cormoran/dya2-keyboard/docs/src/content/docs/build-guide/v1/img/assembly/2_bottom_case_overview.jpeg

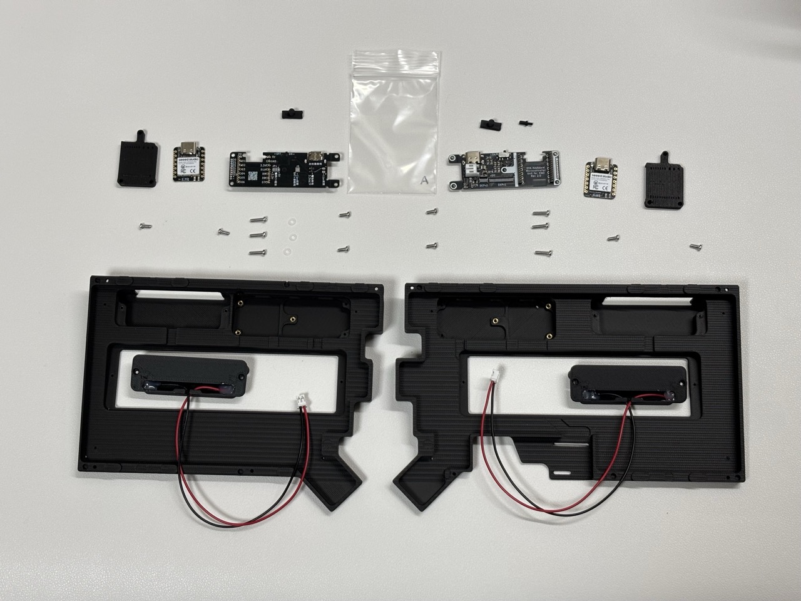
docs/src/content/docs/build-guide/v1/img/assembly/2_bottom_case_overview.jpeg
