cormoran/dya2-keyboard/docs/src/content/docs/build-guide/v1/img/assembly/4_trackball_parts.jpeg

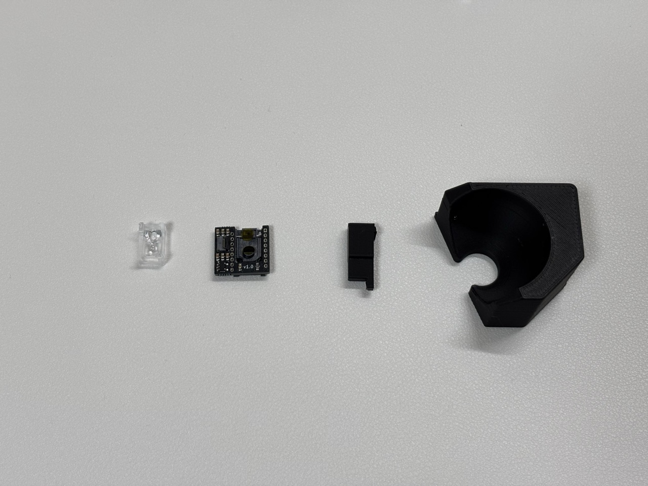
docs/src/content/docs/build-guide/v1/img/assembly/4_trackball_parts.jpeg
