cormoran/dya2-keyboard/docs/src/content/docs/build-guide/v1/img/preparation_electric_parts.jpeg

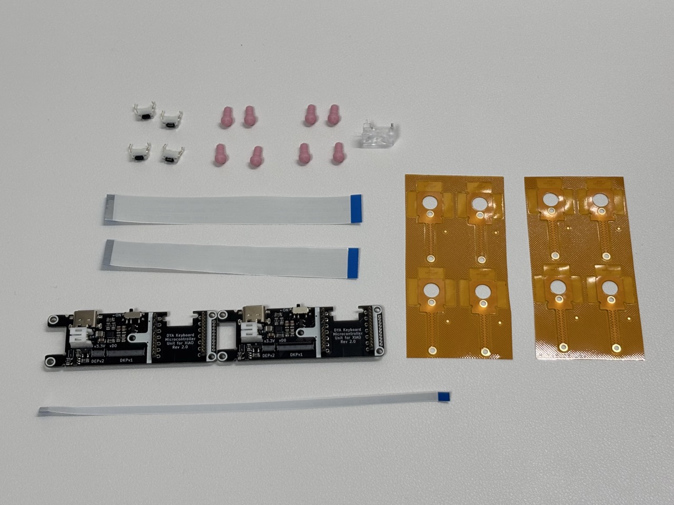
docs/src/content/docs/build-guide/v1/img/preparation_electric_parts.jpeg
