cormoran/dya2-keyboard/docs/src/content/docs/build-guide/v1/img/assembly/1_1_top_plate_separated.jpeg

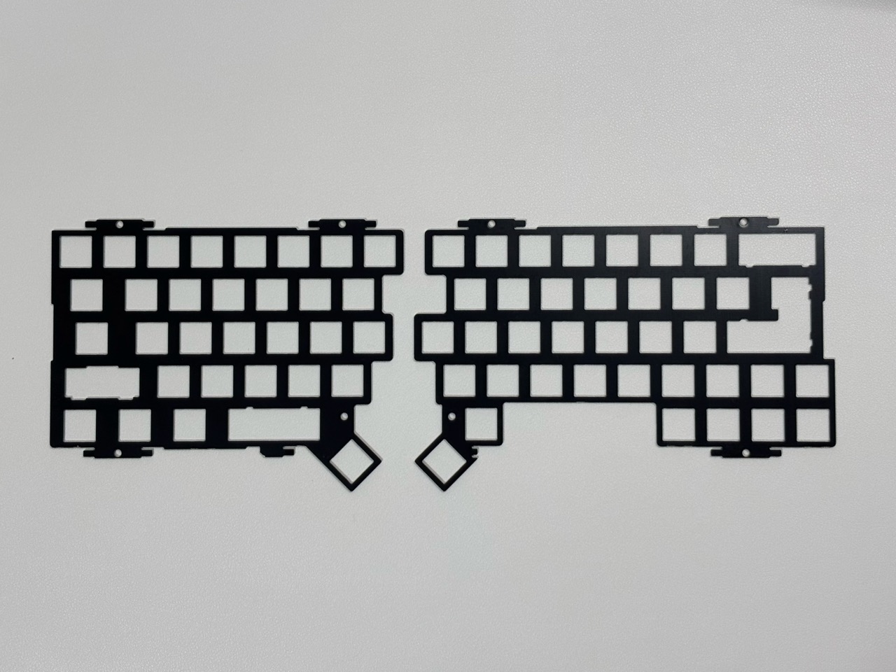
docs/src/content/docs/build-guide/v1/img/assembly/1_1_top_plate_separated.jpeg
