cormoran/dya2-keyboard/docs/src/content/docs/build-guide/v1/img/assembly/1_2_circuit_board_separated.jpeg

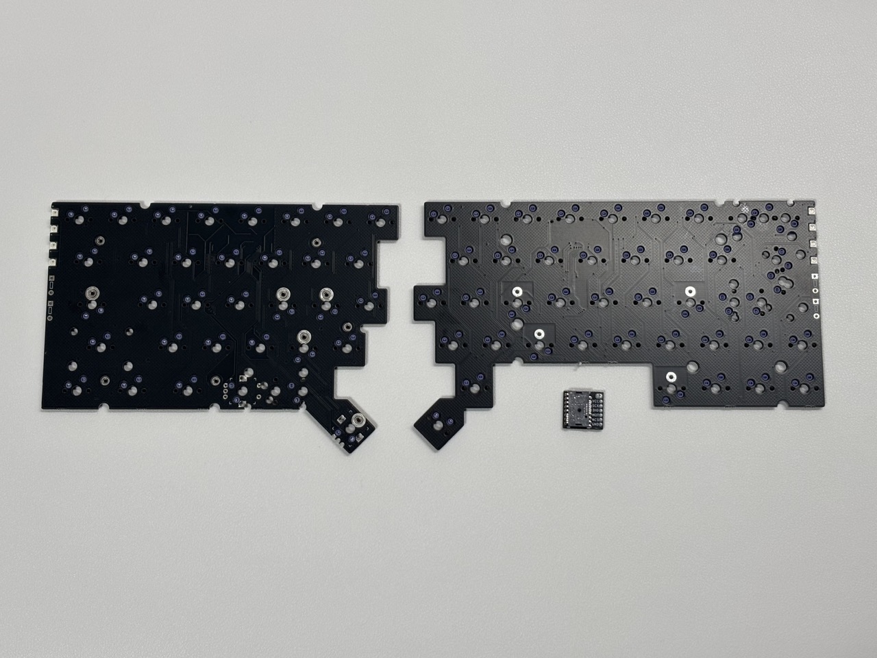
docs/src/content/docs/build-guide/v1/img/assembly/1_2_circuit_board_separated.jpeg
