cormoran/dya2-keyboard/docs/src/content/docs/build-guide/v1/img/assembly/2_1_battery_case.jpeg

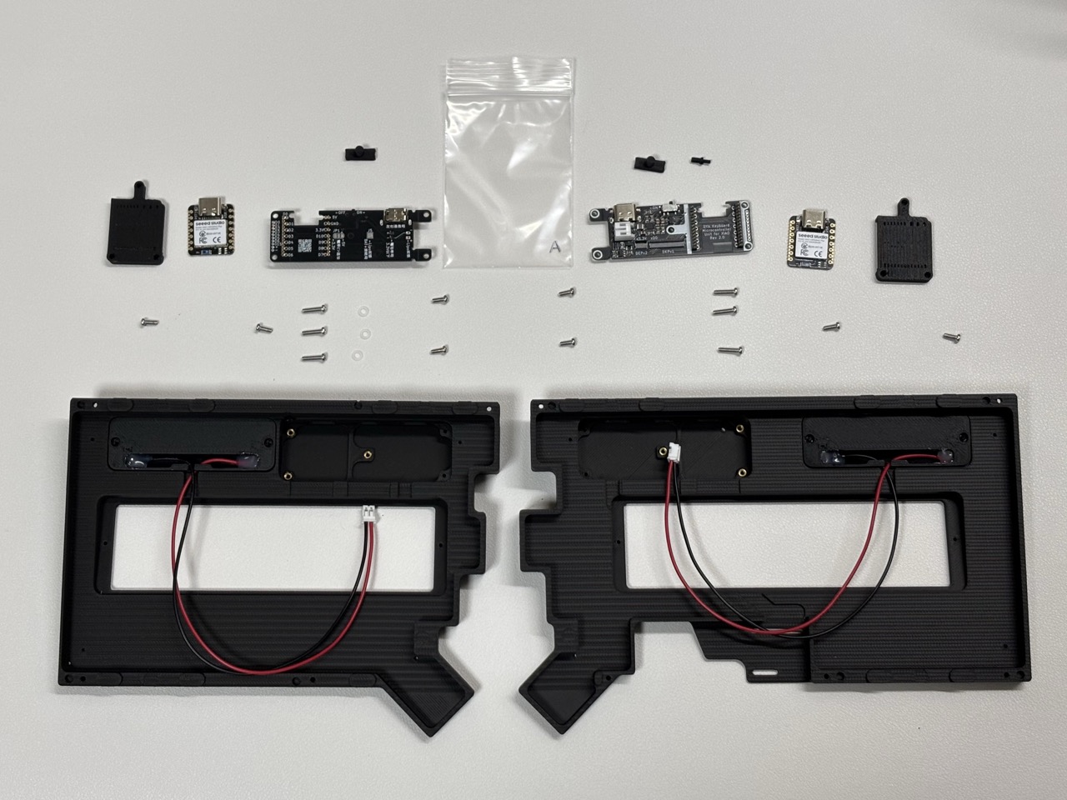
docs/src/content/docs/build-guide/v1/img/assembly/2_1_battery_case.jpeg
