cormoran/dya2-keyboard/docs/src/content/docs/build-guide/v1/img/assembly/2_1_battery_case_screwed.jpeg

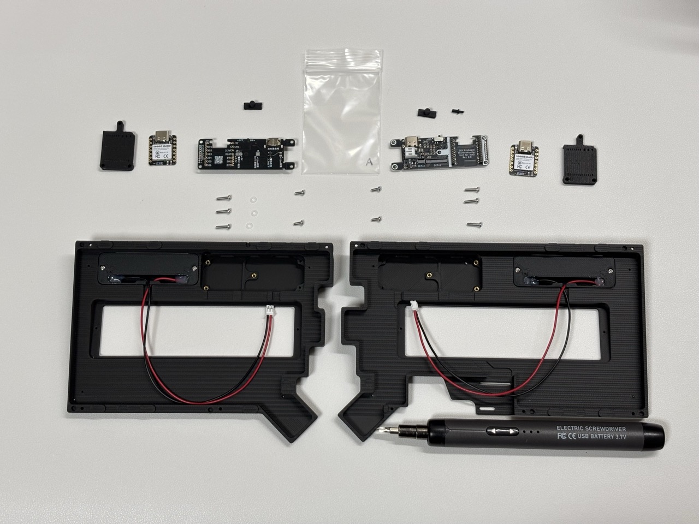
docs/src/content/docs/build-guide/v1/img/assembly/2_1_battery_case_screwed.jpeg
