cormoran/dya2-keyboard/docs/src/content/docs/build-guide/v1/img/assembly/2_2_1_xiao_attached.jpeg

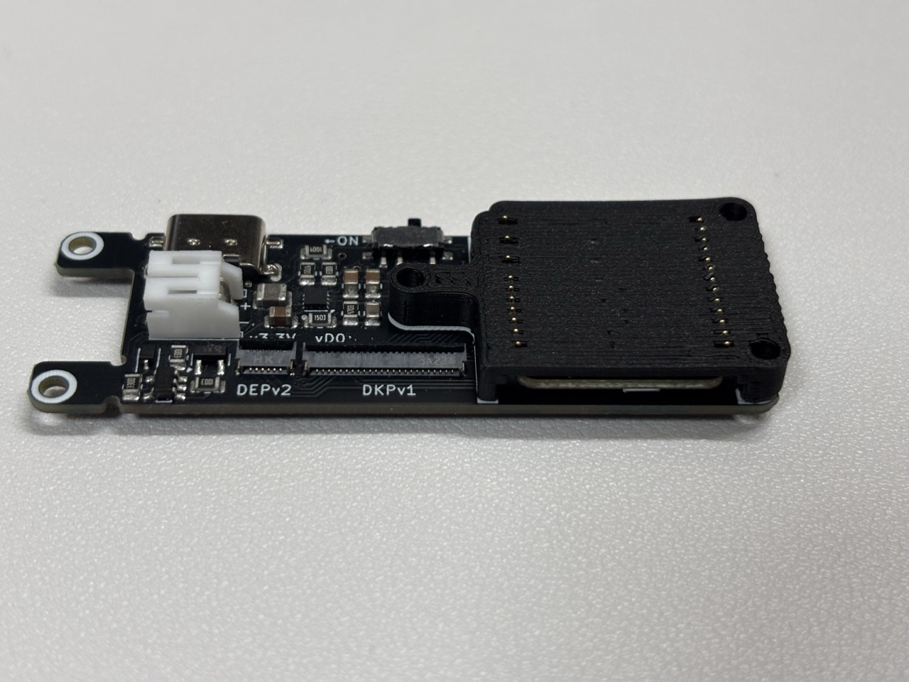
docs/src/content/docs/build-guide/v1/img/assembly/2_2_1_xiao_attached.jpeg
