cormoran/dya2-keyboard/docs/src/content/docs/build-guide/v1/img/assembly/2_2_2_power_sw.jpeg

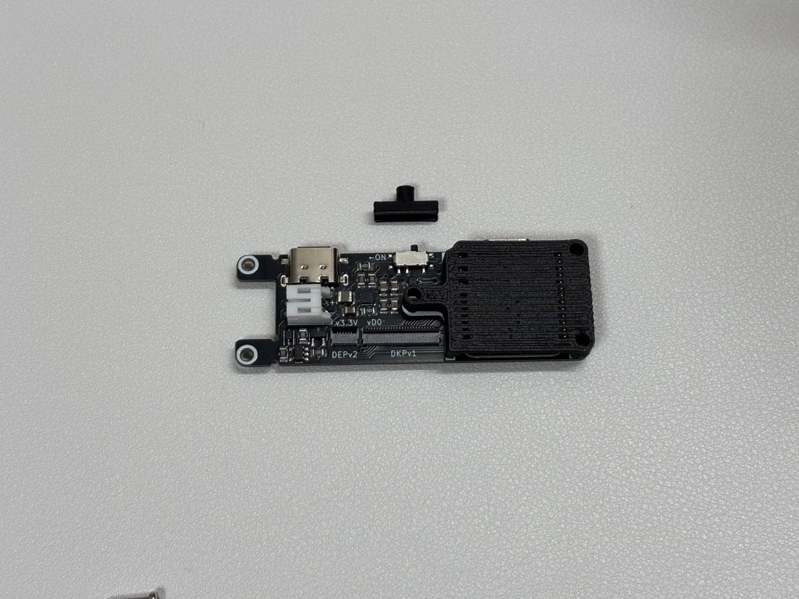
docs/src/content/docs/build-guide/v1/img/assembly/2_2_2_power_sw.jpeg
