cormoran/dya2-keyboard/docs/src/content/docs/build-guide/v1/img/assembly/2_2_3_ffc_left.jpeg

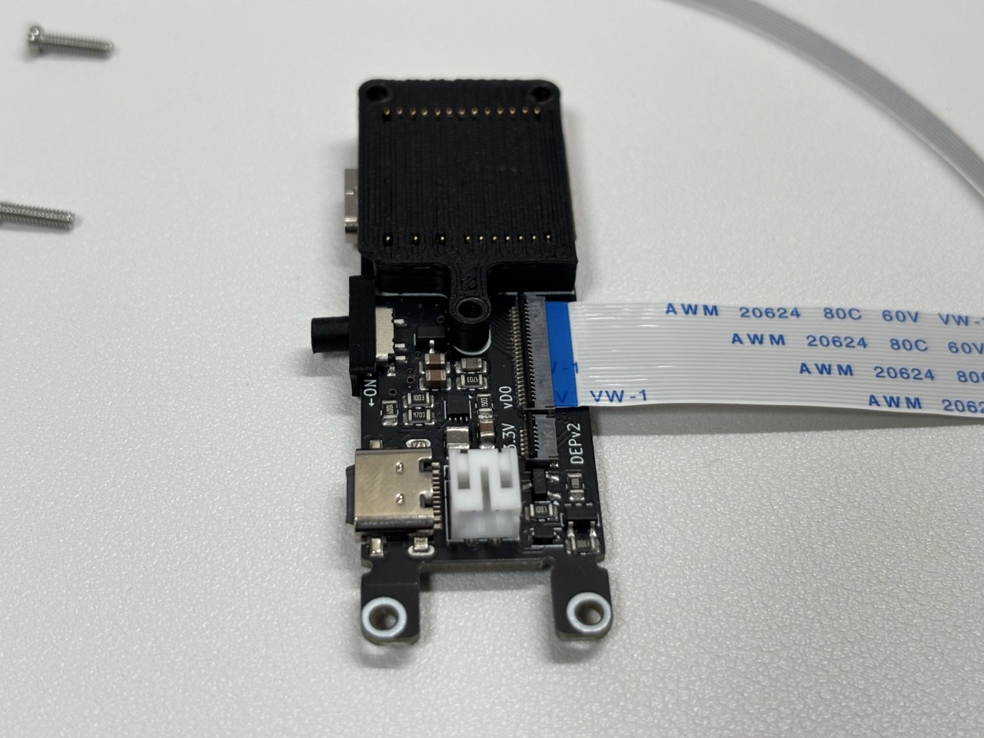
docs/src/content/docs/build-guide/v1/img/assembly/2_2_3_ffc_left.jpeg
