cormoran/dya2-keyboard/docs/src/content/docs/build-guide/v1/img/assembly/2_2_4_reset_button.jpeg

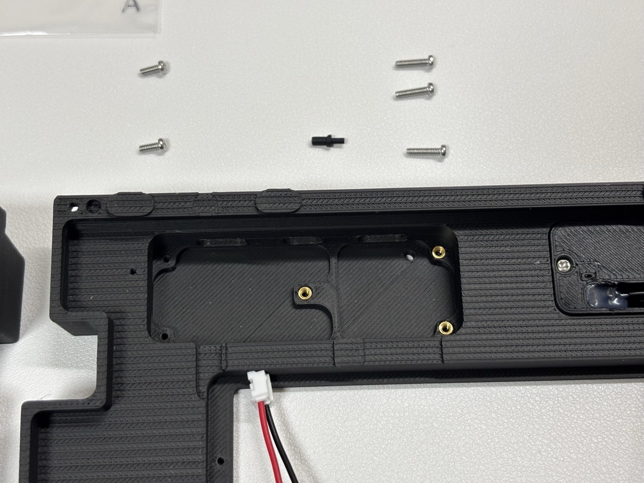
docs/src/content/docs/build-guide/v1/img/assembly/2_2_4_reset_button.jpeg
