cormoran/dya2-keyboard/docs/src/content/docs/build-guide/v1/img/assembly/2_2_5_mount_right.jpeg

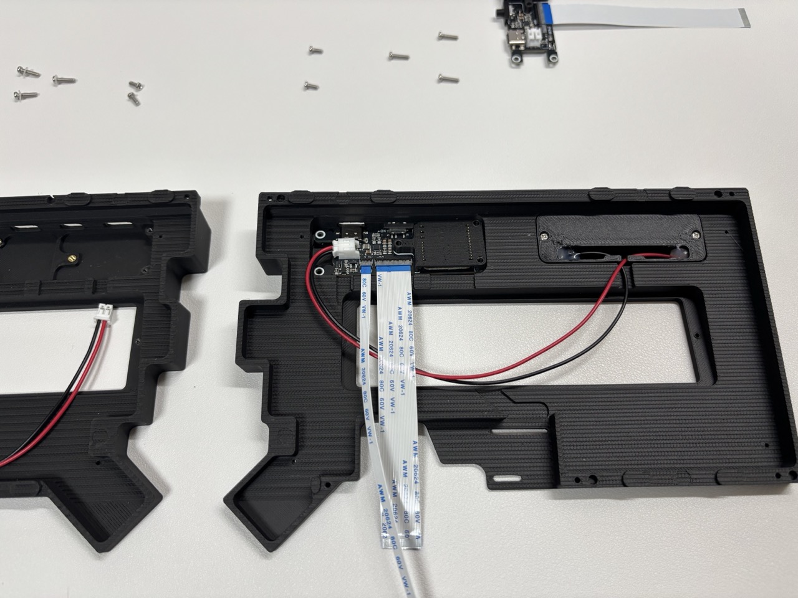
docs/src/content/docs/build-guide/v1/img/assembly/2_2_5_mount_right.jpeg
