cormoran/dya2-keyboard/docs/src/content/docs/build-guide/v1/img/assembly/2_2_6_mount_left_battery.jpeg

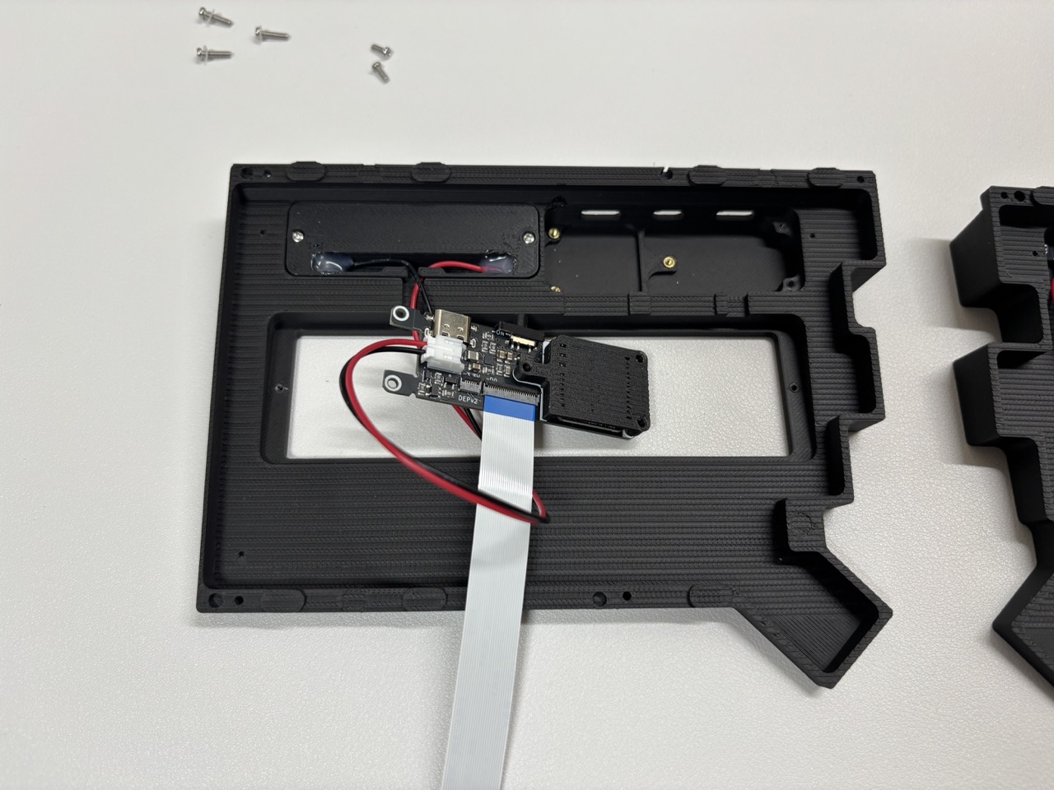
docs/src/content/docs/build-guide/v1/img/assembly/2_2_6_mount_left_battery.jpeg
