cormoran/dya2-keyboard/docs/src/content/docs/build-guide/v1/img/assembly/3_emblem_plate_bottom1.jpeg

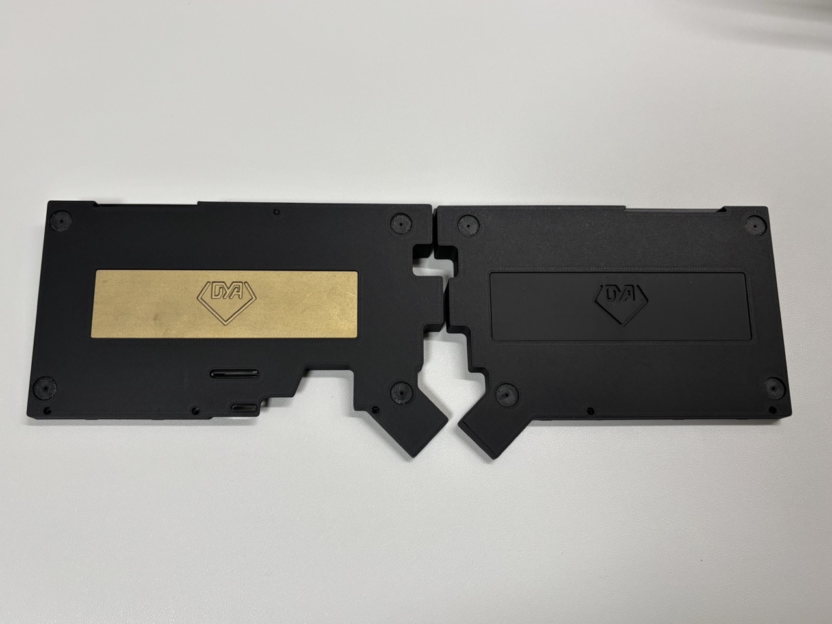
docs/src/content/docs/build-guide/v1/img/assembly/3_emblem_plate_bottom1.jpeg
