cormoran/dya2-keyboard/docs/src/content/docs/build-guide/v1/img/assembly/3_emblem_plate_bottom2.jpeg

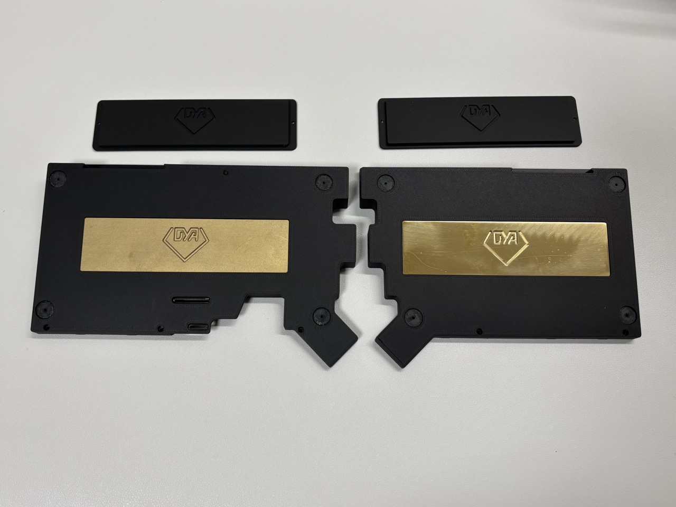
docs/src/content/docs/build-guide/v1/img/assembly/3_emblem_plate_bottom2.jpeg
