cormoran/dya2-keyboard/docs/src/content/docs/build-guide/v1/img/assembly/4_trackball_screw.jpeg

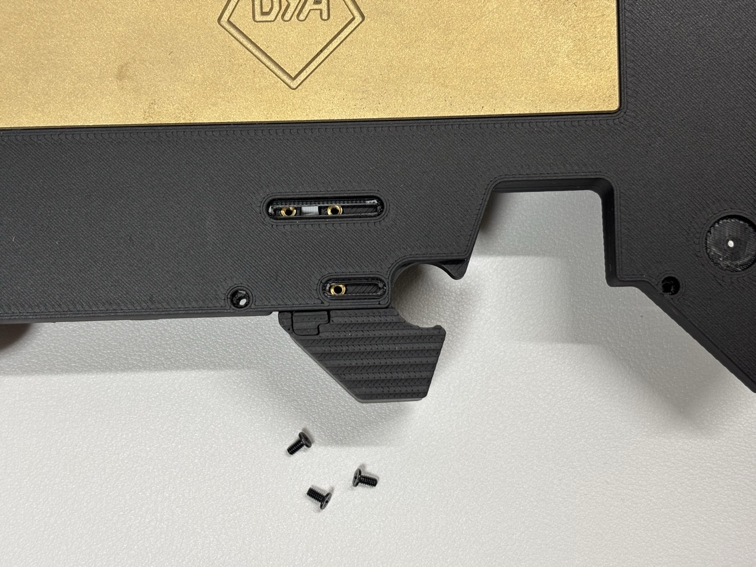
docs/src/content/docs/build-guide/v1/img/assembly/4_trackball_screw.jpeg
