cormoran/dya2-keyboard/docs/src/content/docs/build-guide/v1/img/assembly/5_1_tadpole2.jpeg

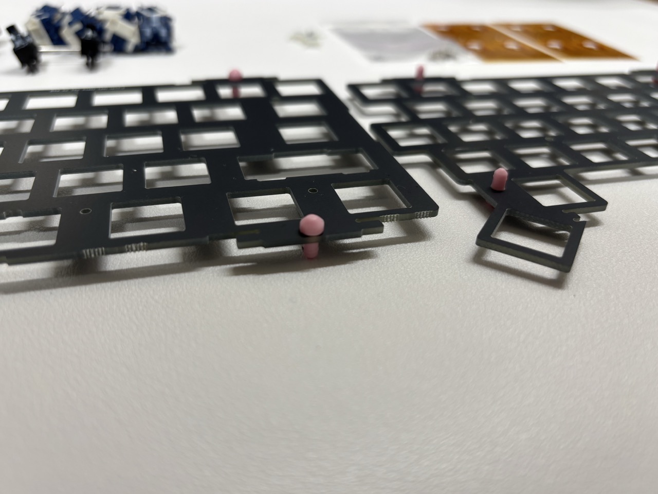
docs/src/content/docs/build-guide/v1/img/assembly/5_1_tadpole2.jpeg
