cormoran/dya2-keyboard/docs/src/content/docs/build-guide/v1/img/assembly/5_2_setting_switch_both.jpeg

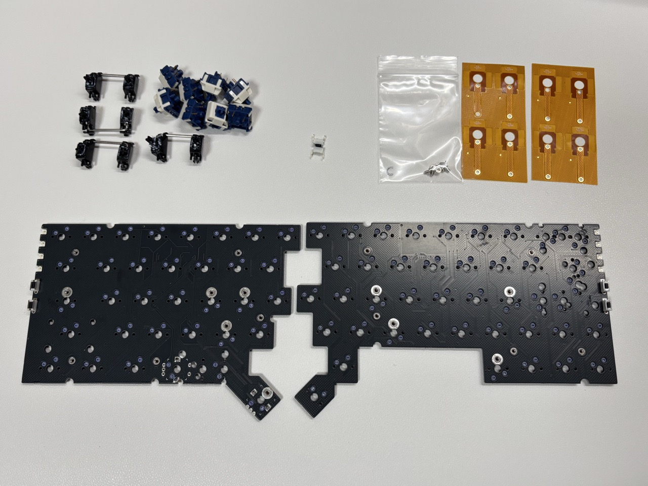
docs/src/content/docs/build-guide/v1/img/assembly/5_2_setting_switch_both.jpeg
