cormoran/dya2-keyboard/docs/src/content/docs/build-guide/v1/img/assembly/5_3_stabilizer_en.jpeg

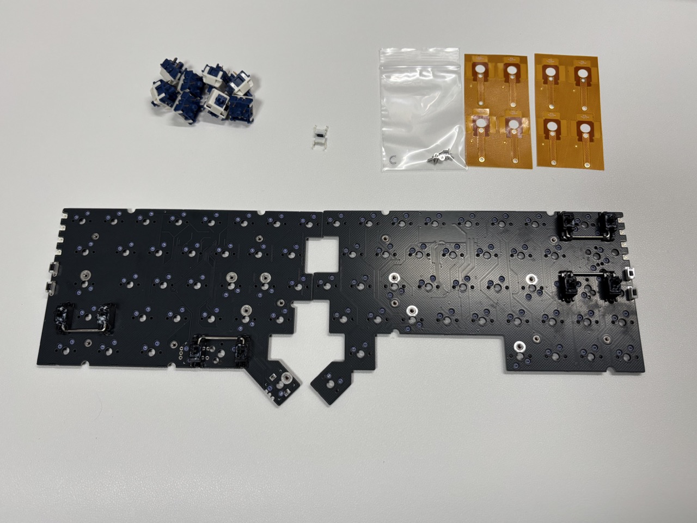
docs/src/content/docs/build-guide/v1/img/assembly/5_3_stabilizer_en.jpeg
