cormoran/dya2-keyboard/docs/src/content/docs/build-guide/v1/img/assembly/5_4_keyswitch_pre2.jpeg

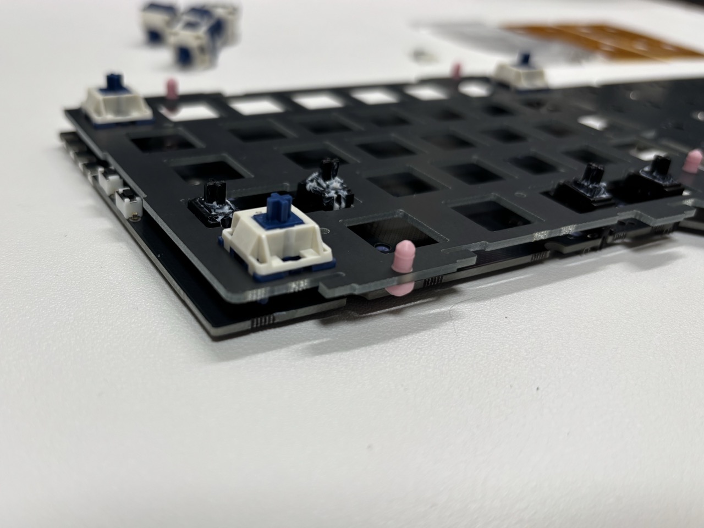
docs/src/content/docs/build-guide/v1/img/assembly/5_4_keyswitch_pre2.jpeg
