cormoran/dya2-keyboard/docs/src/content/docs/build-guide/v1/img/assembly/5_5_touch_sensor_tape2.jpeg

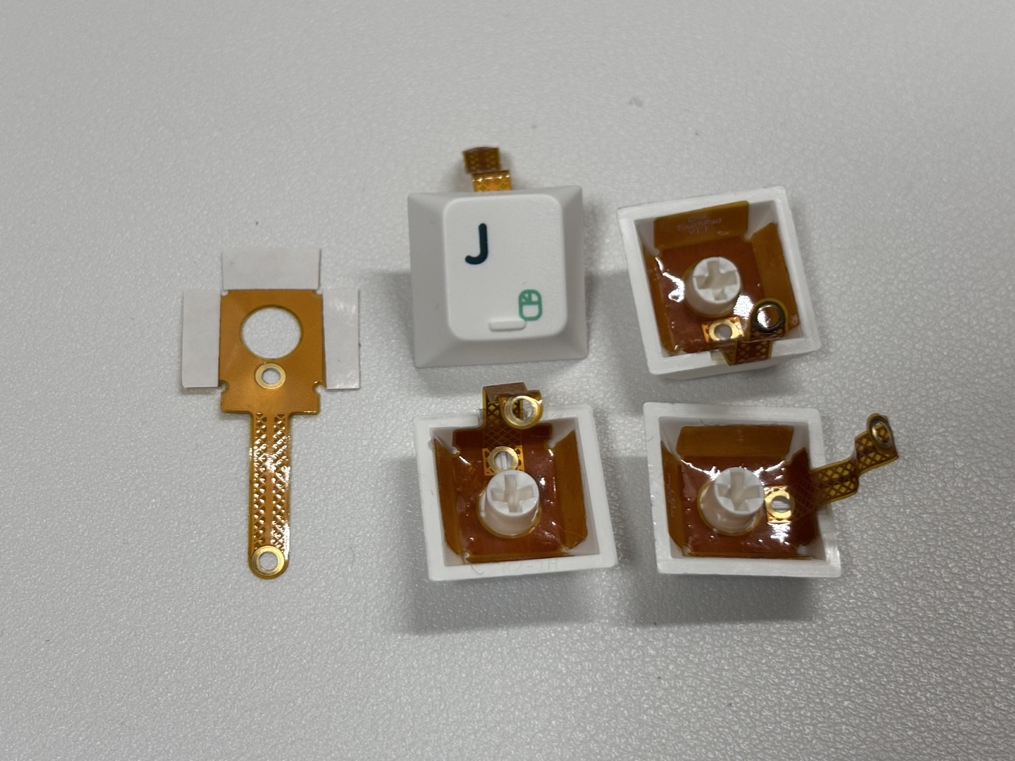
docs/src/content/docs/build-guide/v1/img/assembly/5_5_touch_sensor_tape2.jpeg
