cormoran/dya2-keyboard/docs/src/content/docs/build-guide/v1/img/assembly/5_6_keyswitch_click.jpeg

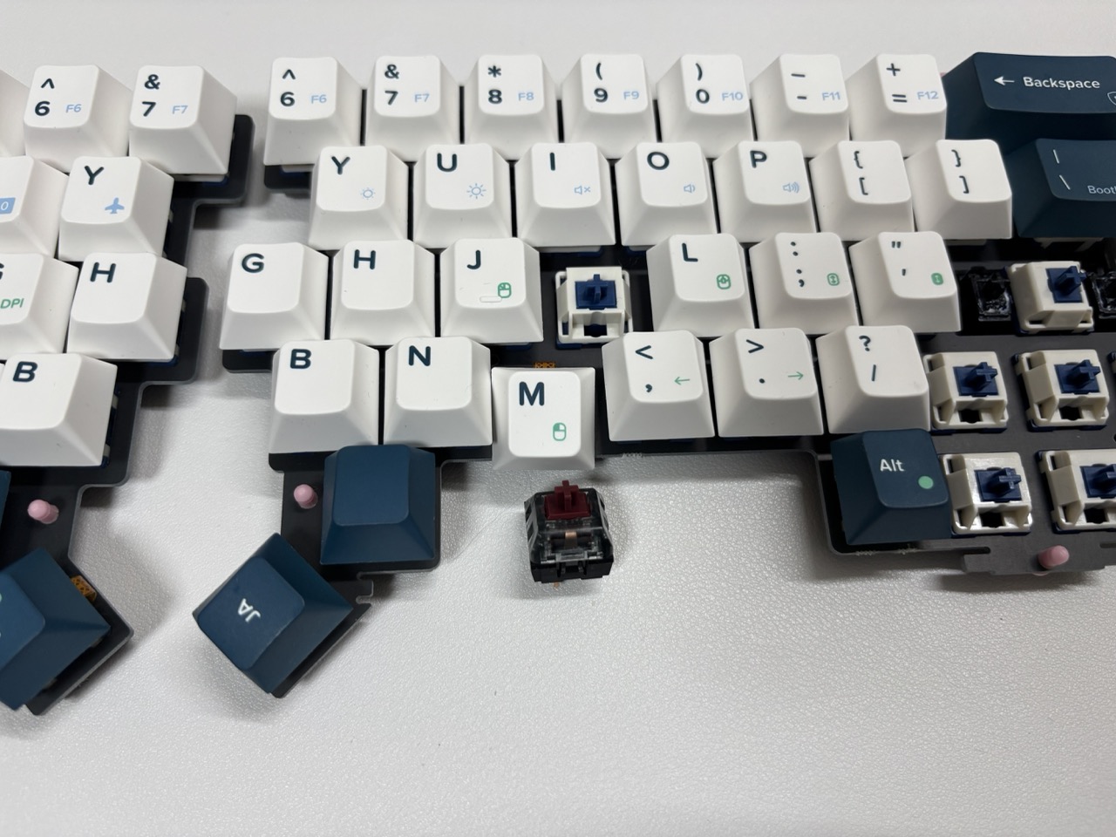
docs/src/content/docs/build-guide/v1/img/assembly/5_6_keyswitch_click.jpeg
