cormoran/dya2-keyboard/docs/src/content/docs/build-guide/v1/img/assembly/5_final.jpeg

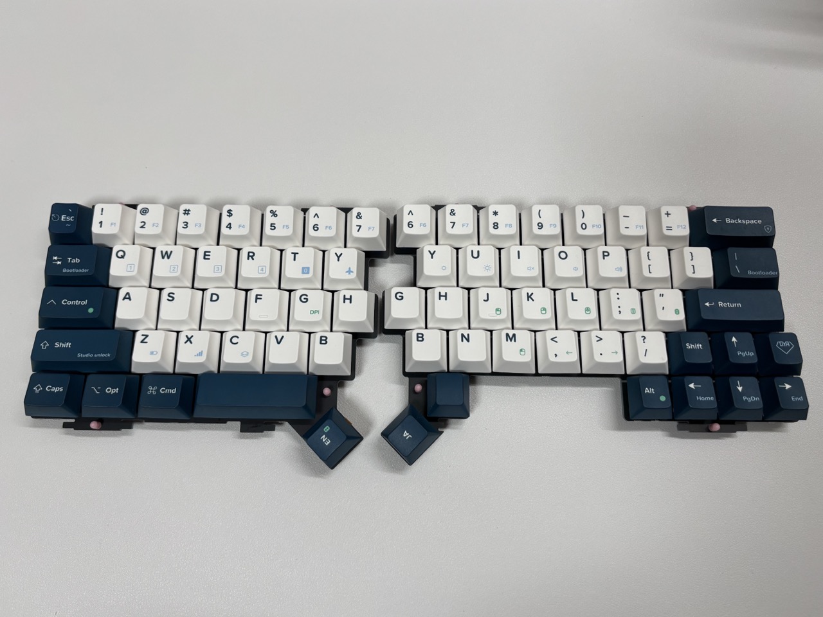
docs/src/content/docs/build-guide/v1/img/assembly/5_final.jpeg
