cormoran/dya2-keyboard/docs/src/content/docs/build-guide/v1/img/assembly/6_1_left_ffc.jpeg

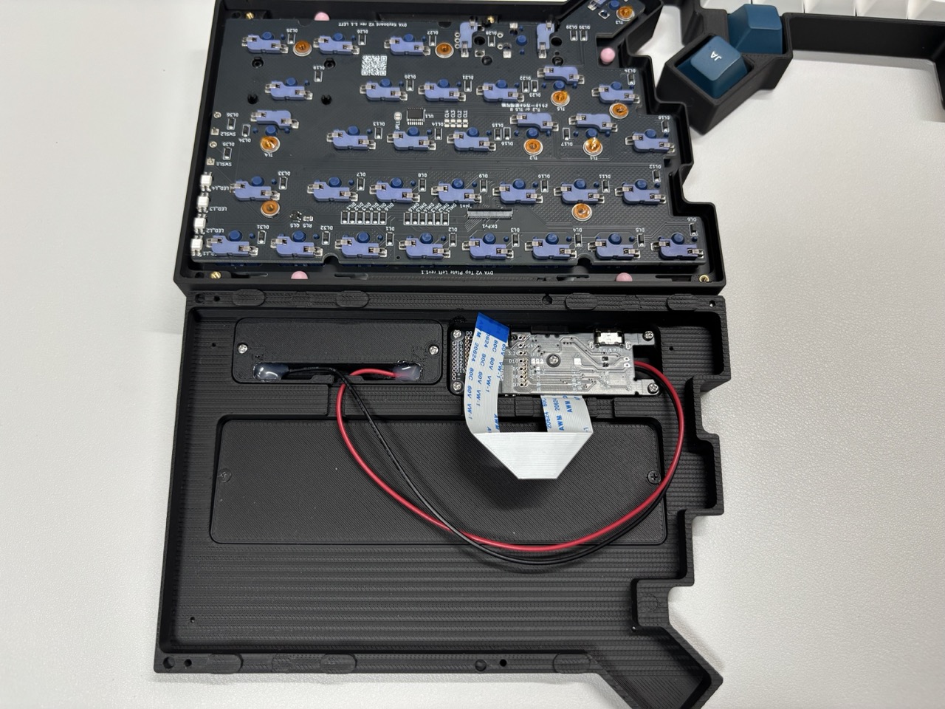
docs/src/content/docs/build-guide/v1/img/assembly/6_1_left_ffc.jpeg
