cormoran/dya2-keyboard/docs/src/content/docs/build-guide/v1/img/assembly/6_2_right_merge.jpeg

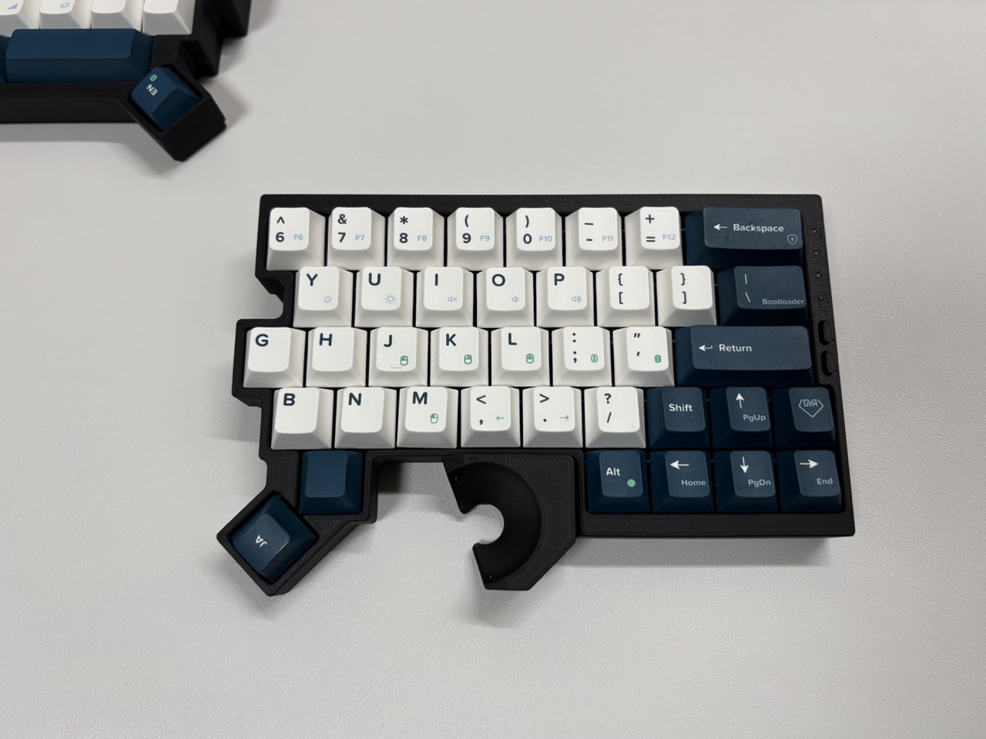
docs/src/content/docs/build-guide/v1/img/assembly/6_2_right_merge.jpeg
