cormoran/dya2-keyboard/docs/src/content/docs/build-guide/v1/img/assembly/6_3_screw2.jpeg

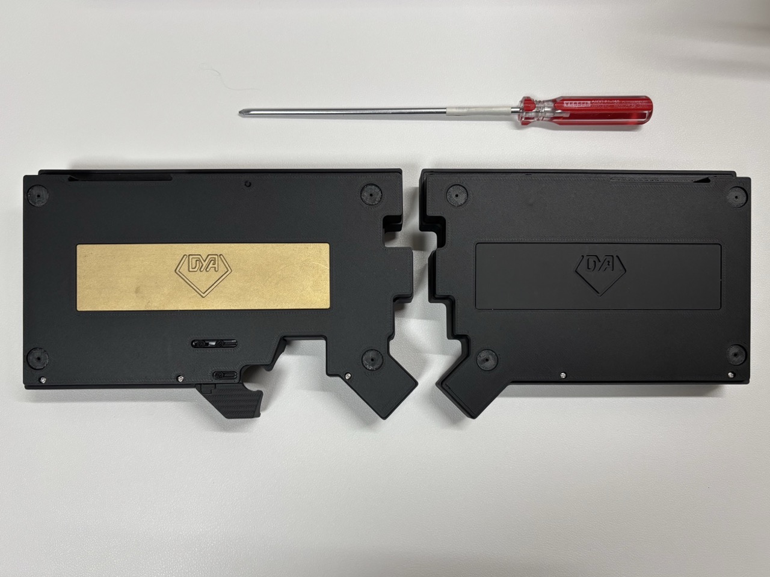
docs/src/content/docs/build-guide/v1/img/assembly/6_3_screw2.jpeg
