cormoran/dya2-keyboard/docs/src/content/docs/build-guide/v1/img/assembly/6_4_pad.jpeg

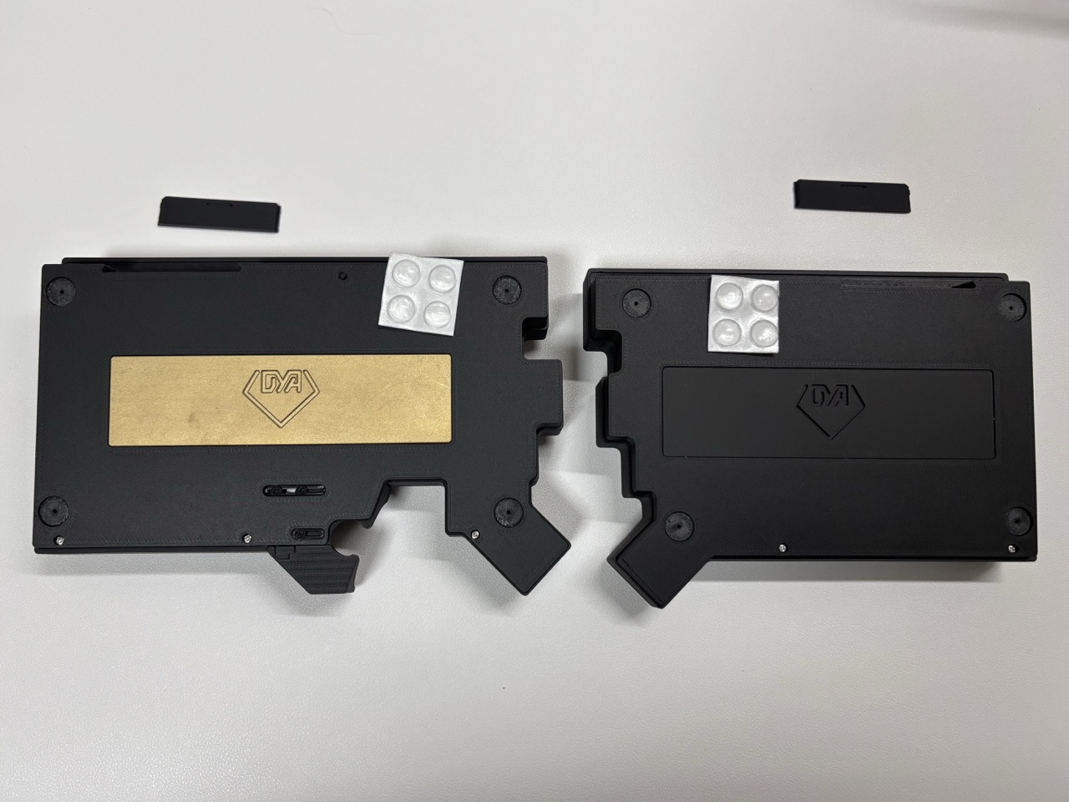
docs/src/content/docs/build-guide/v1/img/assembly/6_4_pad.jpeg
