cormoran/dya2-keyboard/docs/src/content/docs/build-guide/v1/img/assembly/xiao_cut.jpeg

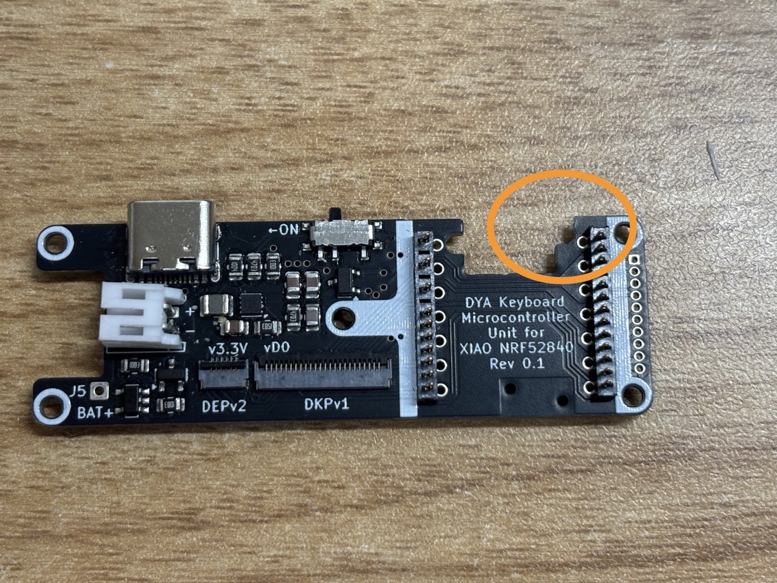
docs/src/content/docs/build-guide/v1/img/assembly/xiao_cut.jpeg
