cormoran/dya2-keyboard/docs/src/content/docs/build-guide/v1/img/preparation_pack.jpeg

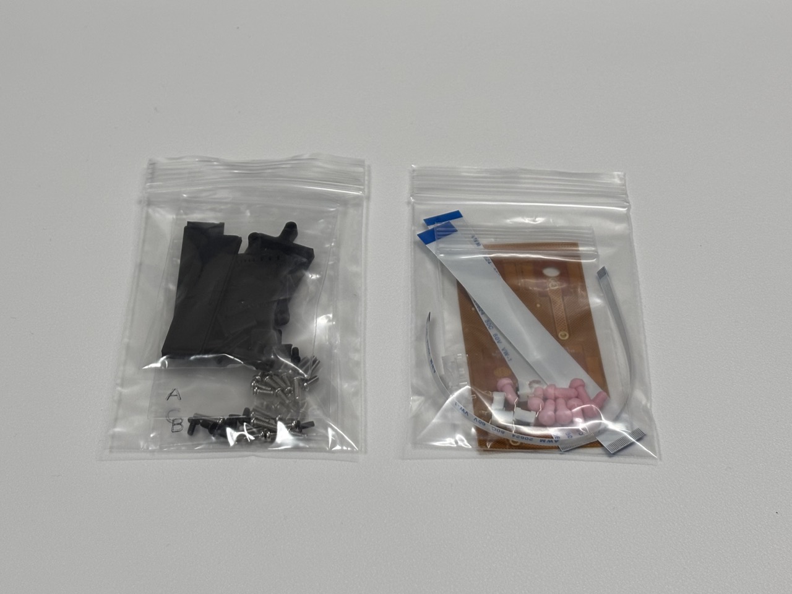
docs/src/content/docs/build-guide/v1/img/preparation_pack.jpeg
