cormoran/dya2-keyboard/docs/src/content/docs/build-guide/v1/img/preparation_trackball2.jpeg

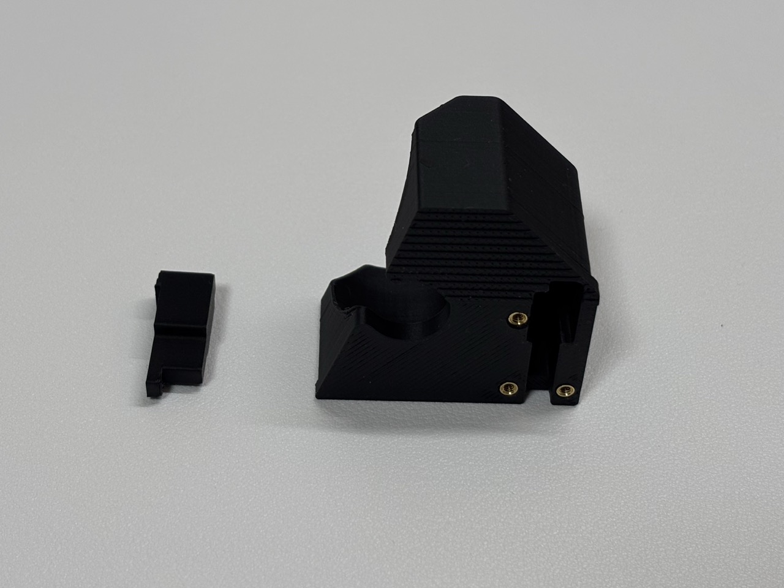
docs/src/content/docs/build-guide/v1/img/preparation_trackball2.jpeg
