cormoran/dya2-keyboard/docs/src/content/docs/feature-guide/img/ble1.jpeg

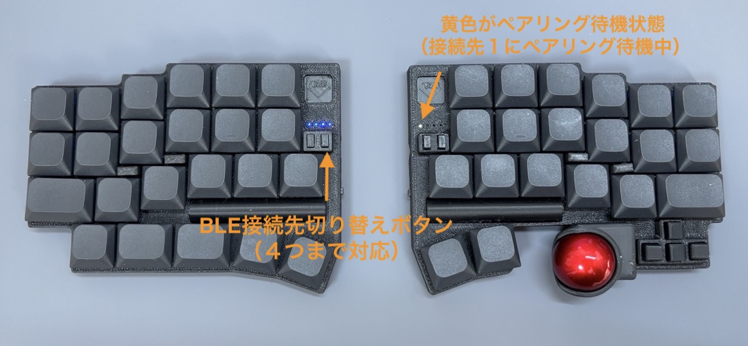
docs/src/content/docs/feature-guide/img/ble1.jpeg
