cormoran/dya2-keyboard/docs/src/content/docs/feature-guide/img/change_default_layer.jpeg

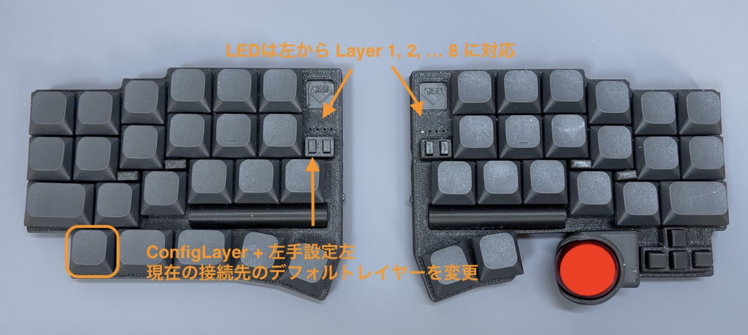
docs/src/content/docs/feature-guide/img/change_default_layer.jpeg
