cormoran/dya2-keyboard/docs/src/content/docs/feature-guide/img/keymap_editor_right_setting.png

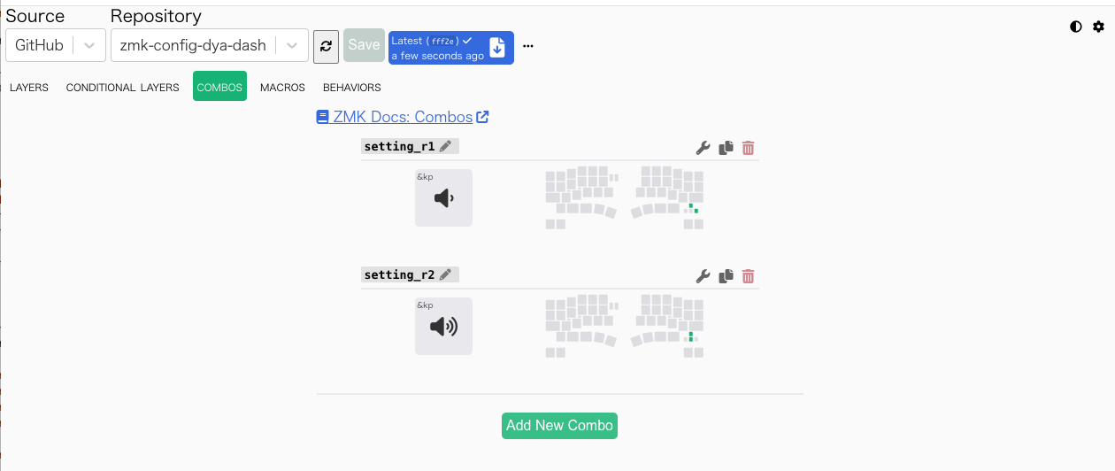
docs/src/content/docs/feature-guide/img/keymap_editor_right_setting.png
